algyan/XIAOGYAN/media/algyan_8th.es2.jpg

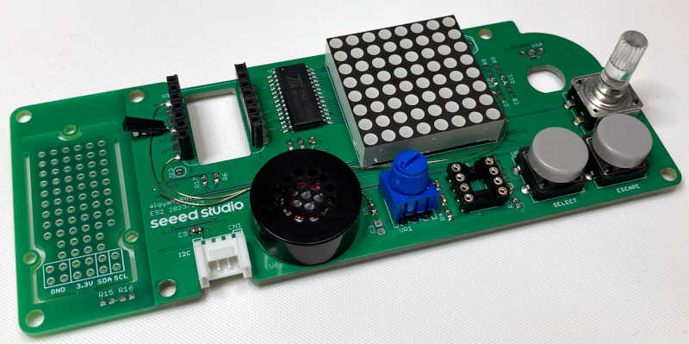
media/algyan_8th.es2.jpg
