algyan/XIAOGYAN/media/algyan_8th.es3.jpg

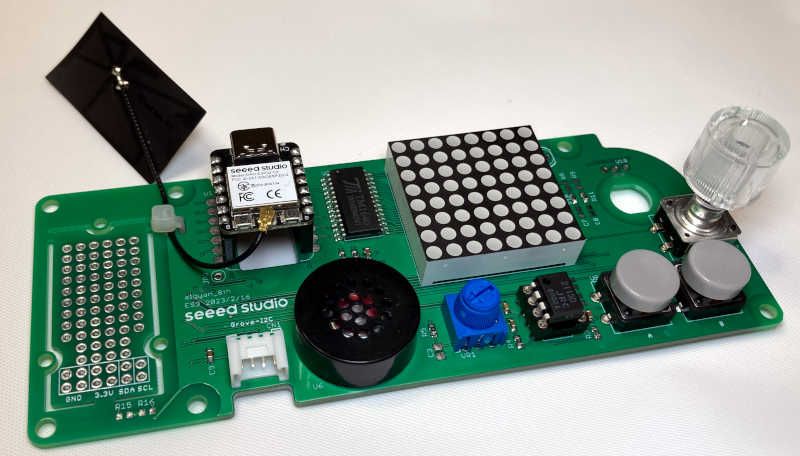
media/algyan_8th.es3.jpg
