algyan/XIAOGYAN/media/algyan_8th.es.jpg

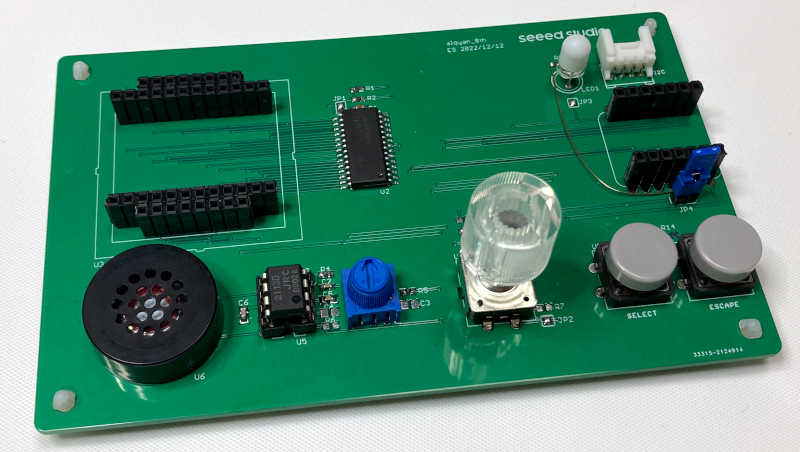
media/algyan_8th.es.jpg
