algyan/XIAOGYAN/manuals/assembly/media/block_diagram.png

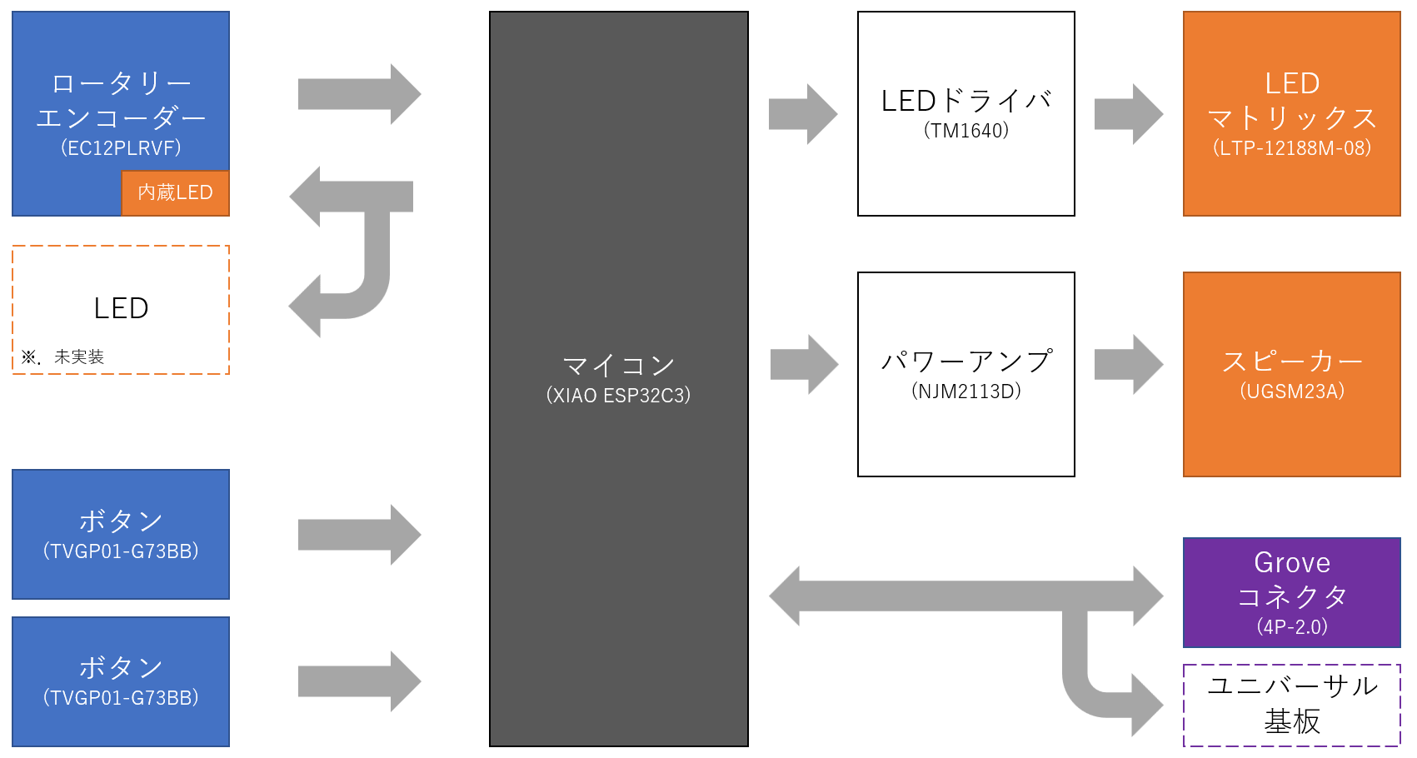
manuals/assembly/media/block_diagram.png
